ItsGosho/8-Bit-Computer/Timer/Comparator.md

TODO: Да вкарам това, което си бях записал
