ItsGosho/8-Bit-Computer/Latches/Old/D Latch Old.md

### Тест 1: (Enable Logic Only without SR Latch)

- Идеята на Enable e че натискаме бутон EN, който позволява бутон D да работи.
- D бутона в конкретният тест активира или Output 1 (O1) или Output 2 (O2).



| D | EN | Output 1 | Output 2 |
| ---- | ---- | --- | --- |
| 0 | 0 | 0 | 0 |
| 0 | 1 | 1 | 0 |
| 1 | 0 | 0 | 0 |
| 1 | 1 | 0 | 1 |

### Тест 2: (Целият D-Latch)



| EN | D | Ouput 1 | Output 2 | Output 3 | Output 4 |
| ---- | ---- | --- | --- | --- | --- |
| 0 | 0 | 0 | 0 | Output 3 | Output 4 |
| 1 | 0 | 1 | 0 | 1 | 0 |
| 0 | 1 | 0 | 0 | Output 3 | Output 4 |
| 1 | 1 | 0 | 1 | 1 | 0 |

Базиране е таблицата върху **Hold EN** -> **Hold/Realese D** -> **Realese EN**.



- При **Hold** на **EN**-a, то *винаги* отиваме в това състояние:

$$
O_3 = 1 \\
O_4 = 0
$$

**Flow Chart:**

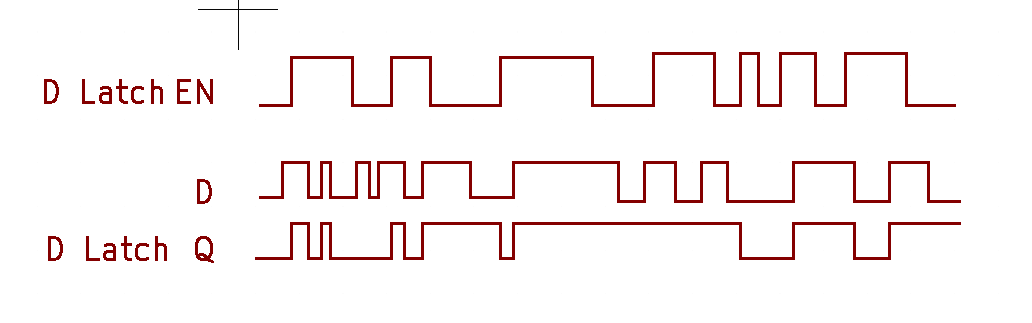
[picture p90: Pictures/image-20220508161237700.png]
