ItsGosho/8-Bit-Computer/Pictures/image-20220522150429415.png

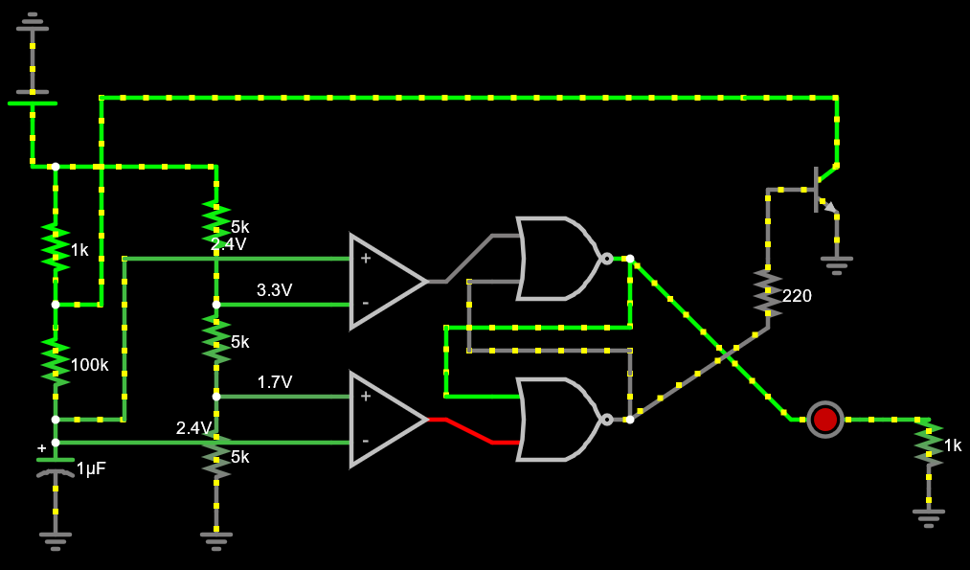
Pictures/image-20220522150429415.png
