ItsGosho/8-Bit-Computer/Pictures/image-20220523023239837.png

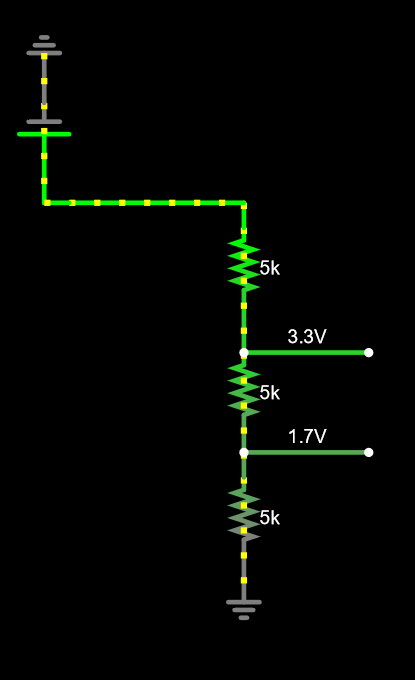
Pictures/image-20220523023239837.png
