ItsGosho/8-Bit-Computer/Pictures/image-20220523024049956.png

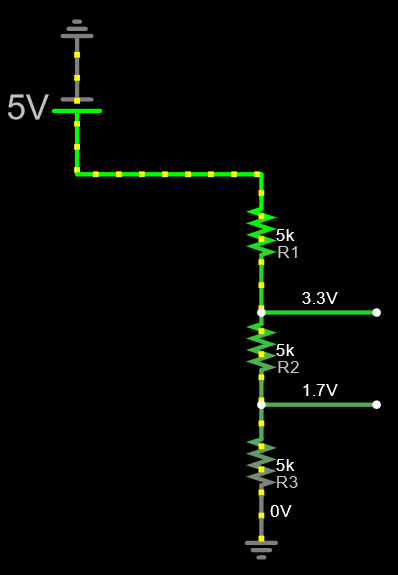
Pictures/image-20220523024049956.png
