ItsGosho/8-Bit-Computer/Pictures/image-20220528161939971.png

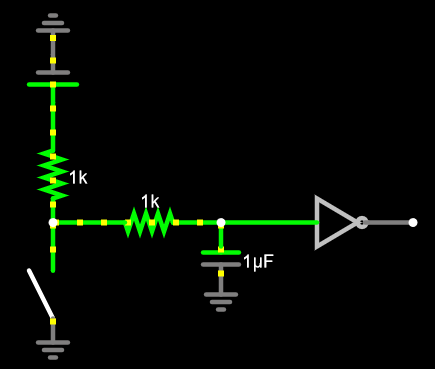
Pictures/image-20220528161939971.png
