ItsGosho/8-Bit-Computer/Pictures/image-20220528210731281.png

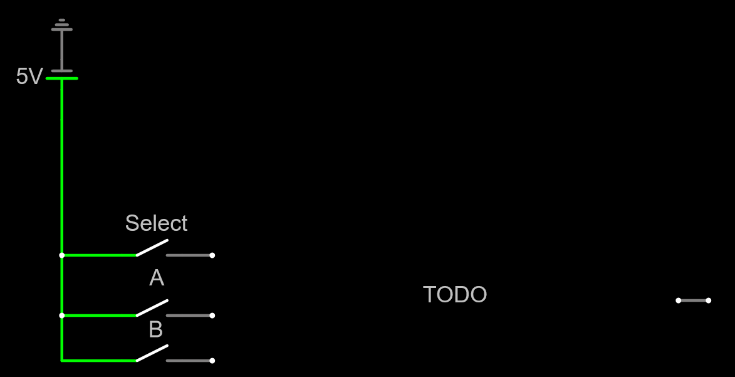
Pictures/image-20220528210731281.png
