ItsGosho/8-Bit-Computer/Pictures/image-20220601030253741.png

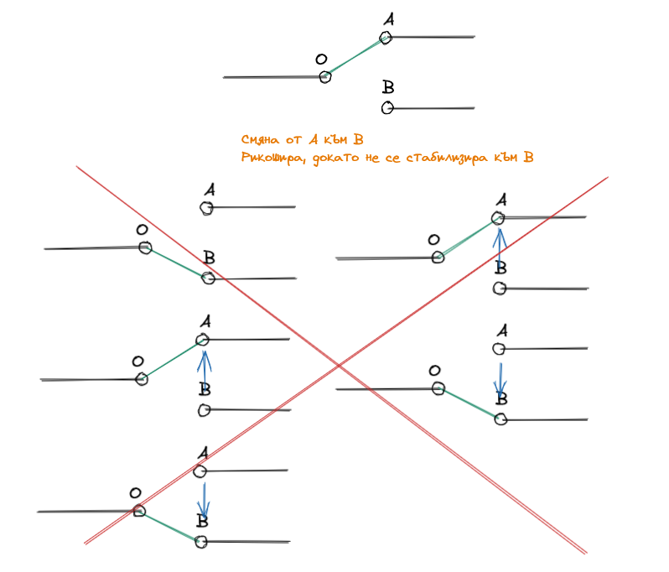
Pictures/image-20220601030253741.png
