ItsGosho/8-Bit-Computer/Pictures/image-20220606155512388.png

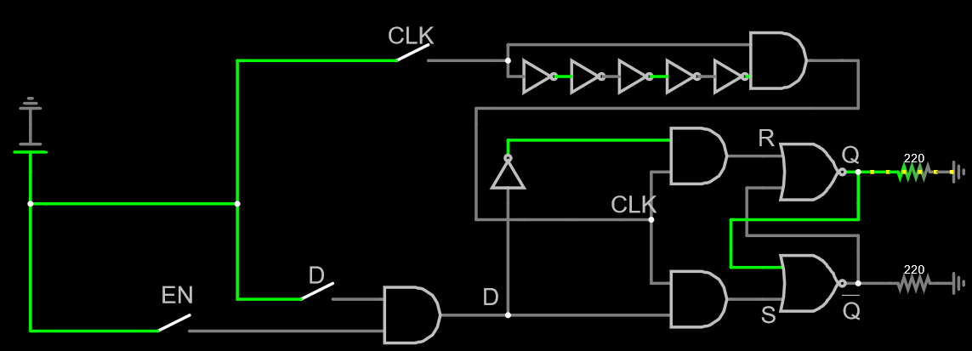
Pictures/image-20220606155512388.png
