ItsGosho/8-Bit-Computer/Pictures/image-20220606174730866.png

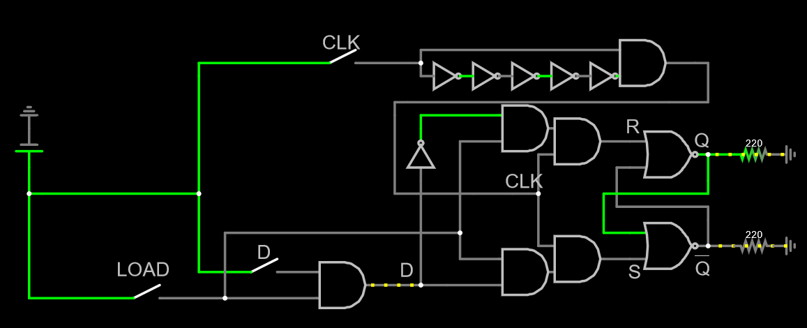
Pictures/image-20220606174730866.png
