ItsGosho/8-Bit-Computer/Pictures/image-20220714164206082.png

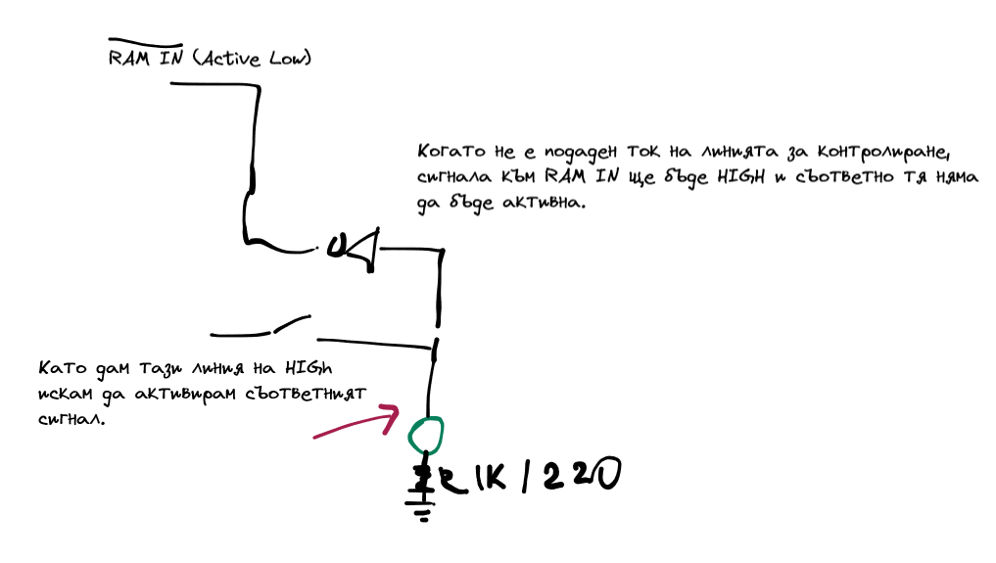
Pictures/image-20220714164206082.png
