ItsGosho/8-Bit-Computer/Pictures/image-20220802163451119.png

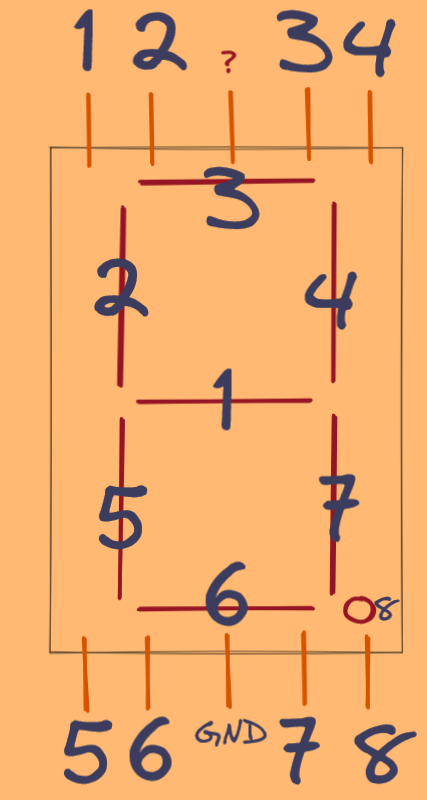
Pictures/image-20220802163451119.png
