ItsGosho/8-Bit-Computer/KiCad Schemantics/simulator_test/Models/uncategorized/BJTNOISE.CIR

BJT Noise Test

*.option temp=200

vcc 4 0 50
vin 1 0 ac

ccouple 1 2 1

ibias 0 2 100uA

rload 4 3 1k

q1 3 2 0 0 test

.model test npn kf=1e-20 af=1 bf=100 rb=10
*.noise v(3) vin dec 10 10 100k 1

.control
destroy all
noise v(3) vin dec 10 10 100k 1
plot noise1.onoise_spectrum
.endc
.end
