ItsGosho/8-Bit-Computer/KiCad Schemantics/simulator_test/Models/uncategorized/CIRCUIT1.CIR

SIMPLE DIFFERENTIAL PAIR

.width out=80
.options nopage

VCC 7 0 12
VEE 8 0 -12
VIN 1 0 AC 1
RS1 1 2 1K
RS2 6 0 1K
Q1 3 2 4 MOD1
Q2 5 6 4 MOD1
RC1 7 3 10K
RC2 7 5 10K
RE 4 8 10K

.MODEL MOD1 NPN BF=50 VAF=50 IS=1.E-12 RB=100 CJC=.5PF TF=.6NS
.TF V(5) VIN
.AC DEC 10 1 100MEG
.PLOT AC VM(5) VP(5)
.PRINT AC VM(5) VP(5)

* Commands for Spice3
*#destroy all
*#run
**#set curplot = ac1
*#plot mag(ac1.v(5)) ph(ac1.v(5))

.END
