ItsGosho/8-Bit-Computer/KiCad Schemantics/simulator_test/Models/uncategorized/CIRCUIT2.CIR

MOS OUTPUT CHARACTERISTICS

.OPTIONS NODE NOPAGE
.width out=80

VDS 3 0
VGS 2 0
M1 1 2 0 0 MOD1 L=4U W=6U AD=10P AS=10P
.MODEL MOD1 NMOS VTO=-2 NSUB=1.0E15 UO=550


* VIDS MEASURES ID, WE COULD HAVE USED VDS, BUT ID WOULD BE NEGATIVE

VIDS 3 1
.DC VDS 0 10 .5 VGS 0 5 1
.PRINT DC I(VIDS) V(2)
.PLOT DC I(VIDS)

* Commands for Spice3
*#destroy all
*#run
*#plot dc1.vids#branch

.END
