ItsGosho/8-Bit-Computer/KiCad Schemantics/simulator_test/Models/uncategorized/CIRCUIT3.CIR

SIMPLE RTL INVERTER

.width out=80

VCC 4 0 5
VIN 1 0 PULSE 0 5 2NS 2NS 2NS 30NS
RB 1 2 10K
Q1 3 2 0 Q1
RC 3 4 1K
.PLOT DC V(3)
.PLOT TRAN V(3) (0,5)
.PRINT TRAN V(3)
.MODEL Q1 NPN BF 20 RB 100 TF .1NS CJC 2PF
.DC VIN 0 5 0.1
.TRAN 1NS 100NS

* Commands for Spice3
*#destroy all
*#run
*#plot dc1.v(3)
*#plot tran1.v(3)

.END
