ItsGosho/8-Bit-Computer/KiCad Schemantics/simulator_test/Models/uncategorized/CIRCUIT5.CIR

TRANSMISSION-LINE INVERTER

.width out=80

V1 1 0 PULSE(0 1 0 0.1N)
R1 1 2 50
X1 2 0 0 4 TLINE
R2 4 0 50
.SUBCKT TLINE 1 2 3 4
T1 1 2 3 4 Z0=50 TD=1.5NS
T2 2 0 4 0 Z0=100 TD=1NS
.ENDS TLINE
.TRAN 0.1NS 20NS
.PLOT TRAN V(2) V(4)

* Commands for Spice3
*#destroy all
*#run
*#plot tran1.v(2) tran1.v(4)

.END
