ItsGosho/8-Bit-Computer/KiCad Schemantics/simulator_test/Models/uncategorized/DIGSR.CIR

* file DIGSR:     CMOS digital shift register test case for SPICE
*
*
*
.options          acct   itl1=300   gmin=1e-11   abstol=1e-9
+                 limpts=205
.width out=133
*
*
.tran  0.2ns   40ns
*
**********************************************************************
*
*      Power supplies
*
*
vd    100    0    dc 5.0
vss   199    0    dc 0.0
*
rcc   100    199    1e6
*
**********************************************************************
*
*     Input wiggles  (piecewise linear waveforms)
*
*
*
vld    210  0     pwl(  0ns 5.0    1ns 5.0    3ns 0v    10ns 0v
*
vldb   220  0     pwl(  0ns 0v    1ns 0v    3ns 5.0    10ns 5.0 )
*
*
vck    250  0     pwl(  0ns 5.0    3ns 5.0    6ns 0v     8ns 0v
+                      11ns 5.0   13ns 5.0   16ns 0v    18ns 0v
+                      21ns 5.0   23ns 5.0   26ns 0v    28ns 0v
+                      31ns 5.0   33ns 5.0   36ns 0v    38ns 0v )
*
vckb   260  0     pwl(  0ns 0v    3ns 0v    6ns 5.0     8ns 5.0
+                      11ns 0v   13ns 0v   16ns 5.0    18ns 5.0
+                      21ns 0v   23ns 0v   26ns 5.0    28ns 5.0
+                      31ns 0v   33ns 0v   36ns 5.0    38ns 5.0 )
*
*
vdin   290  0     pwl(  0ns 0v    6ns 0v    8ns 5.0    16ns 5.0
+                      18ns 0v   26ns 0v   28ns 5.0    36ns 5.0
+                      38ns 0v   40ns 0v )
*
*
*
ra1a   210  0     100K
ra2a   220  0     100K
ra3a   250  0     100K
ra4a   260  0     100K
ra5a   290  0     100K
*
*
.ic    v(301)=0.00
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
m963 100  210   361 199   n   w=20u   l=2u  ad=40p  pd=20u
m964 362  361 100   100   p   w=70u   l=2u  ad=240p pd=45u
m965 362  361 199   199   n   w=35u   l=2u  ad=120p pd=30u
m966 362  260   363 100   p   w=5u    l=2u  ad=40p  pd=20u
m967 362  250   363 199   n   w=5u    l=2u  ad=40p  pd=20u
m968 369  363 100   100   p   w=20u   l=2u  ad=240p pd=45u
m969 369  363 199   199   n   w=10u   l=2u  ad=120p pd=30u
*
*
m970 369  250   371 100   p   w=5u    l=2u  ad=40p  pd=20u
m971 369  260   371 199   n   w=5u    l=2u  ad=40p  pd=20u
m972 199  220   371 100   p   w=5u    l=2u  ad=40p  pd=20u
m973 199  210   371 199   n   w=5u    l=2u  ad=40p  pd=20u
m974 372  371 100   100   p   w=30u   l=2u  ad=240p pd=45u
m975 372  371 199   199   n   w=15u   l=2u  ad=120p pd=30u
m976 372  260   373 100   p   w=5u    l=2u  ad=40p  pd=20u
m977 372  250   373 199   n   w=5u    l=2u  ad=40p  pd=20u
m978 379  373 100   100   p   w=30u   l=2u  ad=240p pd=45u
m979 379  373 199   199   n   w=15u   l=2u  ad=120p pd=30u
*
*
m980 379  250   381 100   p   w=5u    l=2u  ad=40p  pd=20u
m981 379  260   381 199   n   w=5u    l=2u  ad=40p  pd=20u
m982 100  220   381 100   p   w=5u    l=2u  ad=40p  pd=20u
m983 100  210   381 199   n   w=5u    l=2u  ad=40p  pd=20u
m984 382  381 100   100   p   w=30u   l=2u  ad=240p pd=45u
m985 382  381 199   199   n   w=15u   l=2u  ad=120p pd=30u
m986 382  260   383 100   p   w=5u    l=2u  ad=40p  pd=20u
m987 382  250   383 199   n   w=5u    l=2u  ad=40p  pd=20u
m988 389  383 100   100   p   w=30u   l=2u  ad=240p pd=45u
m989 389  383 199   199   n   w=15u   l=2u  ad=120p pd=30u
*
*
*
*
**********************************************************************
*
*      Outputs (raw output from Spice)
*
*
*
*
.print   tran  v(309)   v(319)   v(339)   v(349)
+              v(359)   v(369)   v(379)   v(389)
*
*
*
**********************************************************************
*
*   MOS model parameters for 2 micron CMOS
*
.model n nmos
+   level=2        vto=0.7        tox=400e-10
+   nsub=9e15      xj=0.15u       ld=0.20u
+   uo=666         ucrit=.65e5    uexp=0.123
+   vmax=5e4       neff=4.0       delta=1.4
+   rsh=36         cgso=200p      cgdo=200p
+   cj=200u        cjsw=500p      mj=0.75
+   mjsw=0.30      pb=0.80        nfs=1e11
*
*
.model p pmos
+   level=2        vto=-0.70      tox=400e-10
+   nsub=7e15      xj=0.06u       ld=0.20u
+   uo=250         ucrit=.85e5    uexp=0.3
+   vmax=3e4       neff=2.65      delta=1.0
+   rsh=100        cgso=190p      cgdo=190p
+   cj=250u        cjsw=350p      mj=.55
+   mjsw=0.34      pb=0.80        nfs=1e11
*
**********************************************************************
*
*
*
*
.end
