ItsGosho/8-Bit-Computer/KiCad Schemantics/ram_write_signal_fix/ram_write_signal_fix.kicad_pcb

## KiCad design Circuit KiCAD/Pedal turner circuit/Pedal turner circuit.kicad_sch

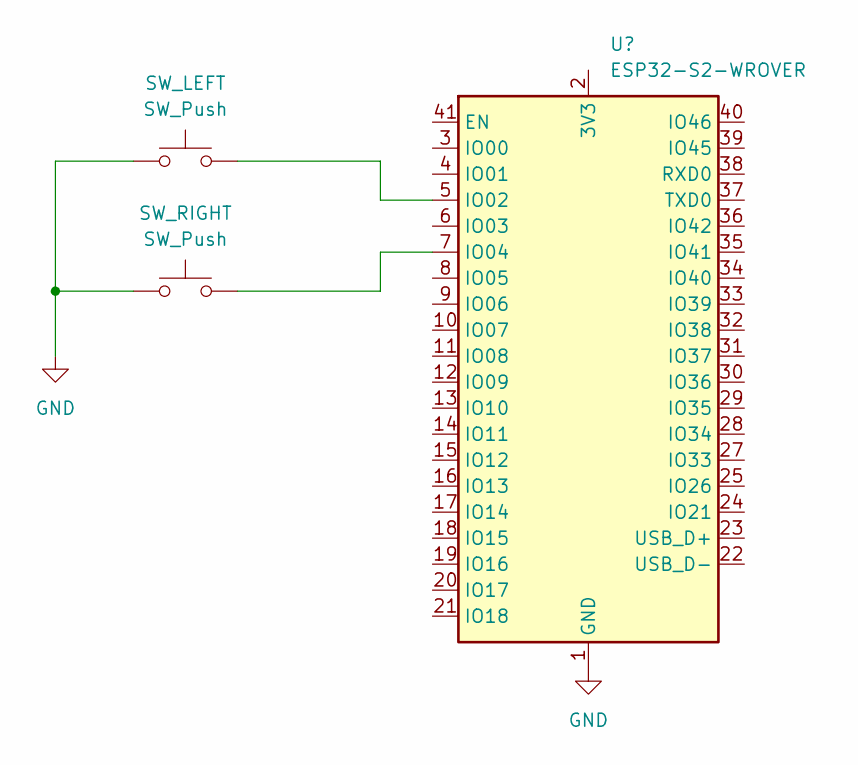
[picture p102: schematic Pedal turner circuit.kicad_sch]

Parts:
SW_LEFT: SW_Push
SW_RIGHT: SW_Push

Connections:
unnamed: SW_LEFT.1, SW_RIGHT.1
